fdiebel/lomo-primes-ff/img/01.jpg

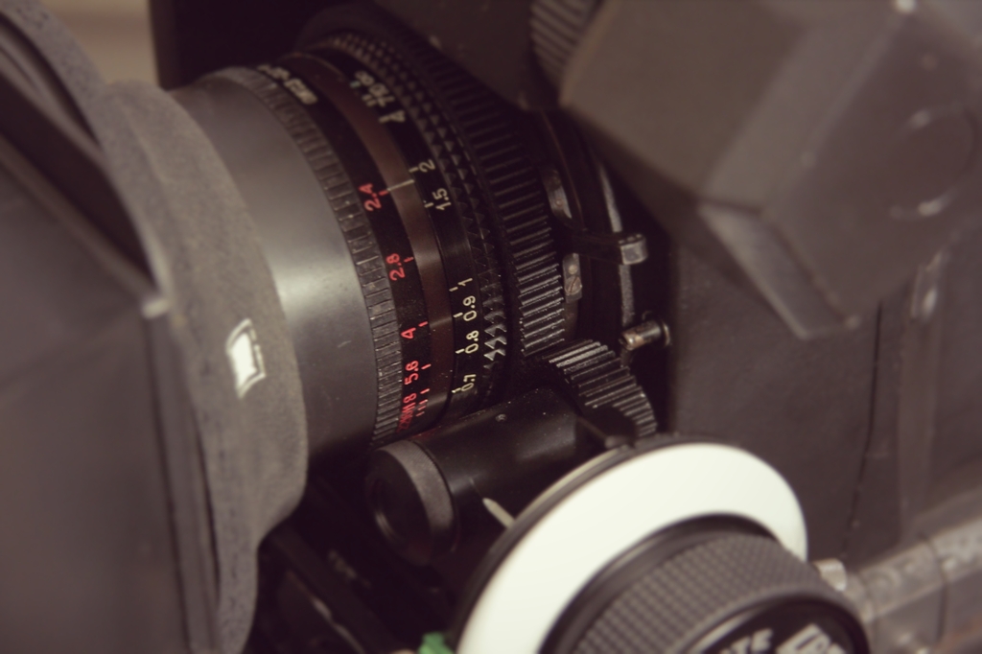
img/01.jpg
