fdiebel/lomo-primes-ff/img/02.jpg

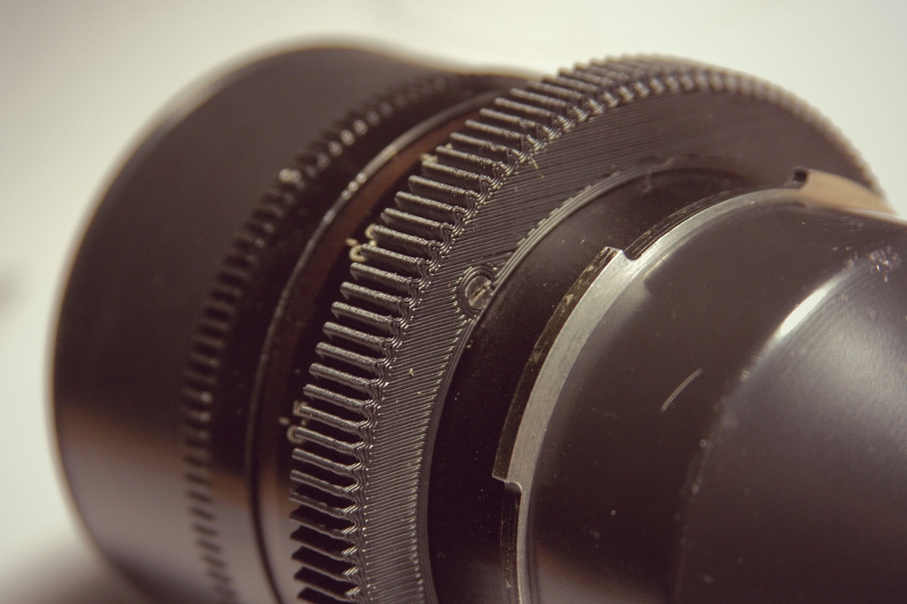
img/02.jpg
