fdiebel/lomo-primes-ff/img/03.jpg

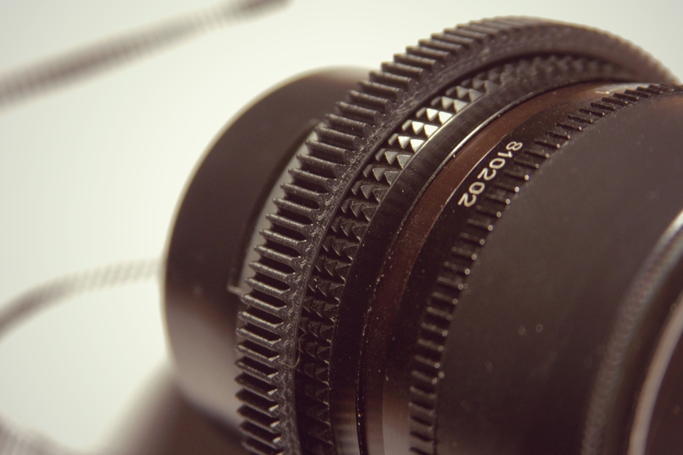
img/03.jpg
