fdiebel/lomo-primes-ff/img/04.jpg

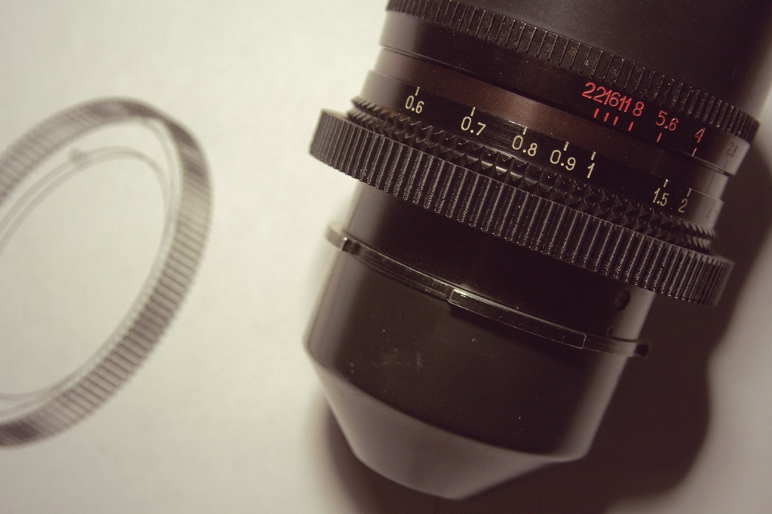
img/04.jpg
