fdiebel/lomo-primes-ff/img/06.jpg

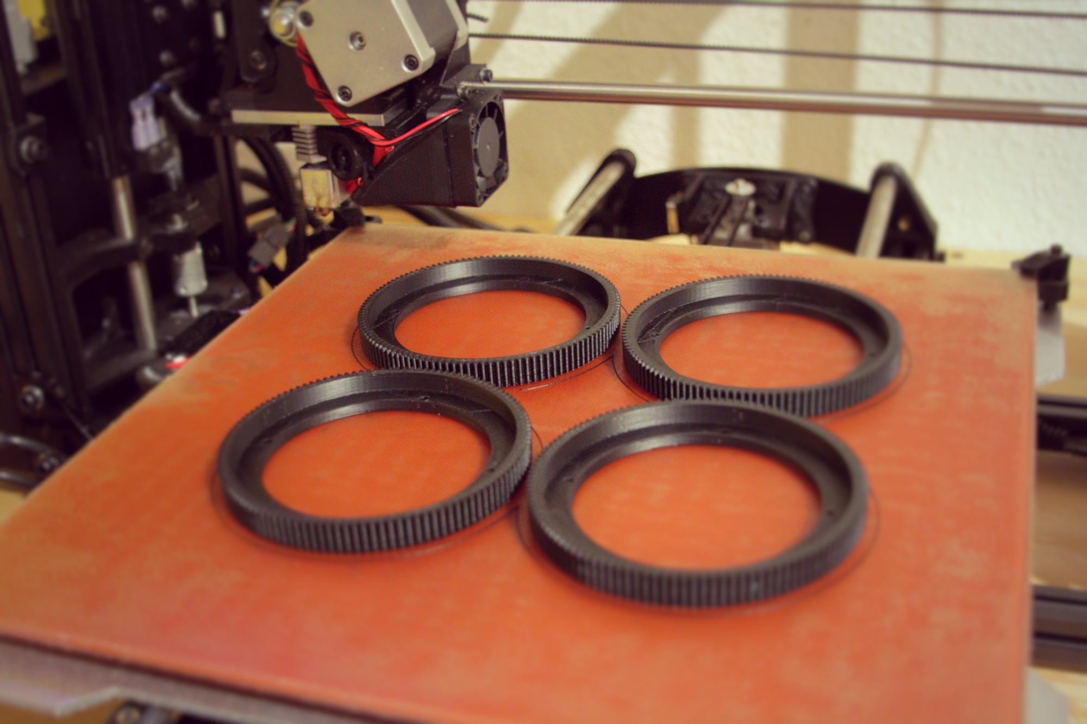
img/06.jpg
